locked/picoclock/3d-mini/screen_holder.scad

include <common.scad>;

border_width = 3;
border_height = 1.5;


module support() {
    cube(screen_holder_in, center=true);

    translate([0, 0]) cube([screen_holder_in[0], screen_holder_out[1], screen_holder_in[2]], center=true);
    // 2 holders

    // 4 screw supports
    $x = screen_holder_in[0]/2-screen_holder_out[0]/2;
    $y = -screen_holder_out[1]/2+screen_holder_out[0]/2;
    $z = -screen_holder_out[2];
    translate([$x, $y, $z])
        cube([screen_holder_out[0], screen_holder_out[0], screen_holder_out[2]], center=true);
    $y2 = screen_holder_out[1]/2-screen_holder_out[0]/2;
    translate([$x, $y2, $z])
        cube([screen_holder_out[0], screen_holder_out[0], screen_holder_out[2]], center=true);
    translate([-screen_holder_in[0]/2+screen_holder_out[0]/2, -screen_holder_out[1]/2+screen_holder_out[0]/2, -screen_holder_out[2]])
        cube([screen_holder_out[0], screen_holder_out[0], screen_holder_out[2]], center=true);
    translate([-screen_holder_in[0]/2+screen_holder_out[0]/2, screen_holder_out[1]/2-screen_holder_out[0]/2, -screen_holder_out[2]])
        cube([screen_holder_out[0], screen_holder_out[0], screen_holder_out[2]], center=true);

    // Support for printing
    for (x = [0:3]) {
        $posy = x < 2 ? -screen_holder_out[1]/2 + screen_holder_out[0]: screen_holder_out[1]/2;
        $mirrorz = x % 2 == 0 ? 1 : 0;
        mirror([$mirrorz,0,0])
            translate([
                -screen_holder_in[0]/2+screen_holder_out[0],
                $posy,
                -screen_holder_out[2]/2])
                rotate([90, 90])
                    linear_extrude(screen_holder_out[0])
                        polygon(points=[[0,0], [screen_holder_out[2], 0], [0, screen_holder_out[0]-1]], paths=[[0,1,2]]);
    }

    // Pins toward PCB
    for (x = [0:1]) {
        for (y = [0:1]) {
            translate([
                (x == 0 ? 1 : -1) * screen_holder_in[0]/2 + (x == 0 ? -1 : 1) * screen_holder_out[0]/2,
                (y == 0 ? 1 : -1) * screen_holder_out[1]/2 + (y == 0 ? -1 : 1) * screen_holder_screw_rad + (y == 0 ? -1 : 1) * 1,
                -screen_holder_out[2]-2-1.5])
            cylinder(h=2, d=1.9, $fn=20);
        }
    }

    // Blocks for case pins
    case_pin_height = 3.5;
    difference() {
        union() {
            for (x = [0:1]) {
                for (y = [0:1]) {
                    translate([
                        (x == 0 ? 1 : -1) * screen_holder_in[0]/2 + (x == 0 ? -1 : 1) * screen_holder_out[0]/2,
                        (y == 0 ? 1 : -1) * screen_holder_out[1]/2 + (y == 0 ? -1 : 1) * screen_holder_screw_rad + (y == 0 ? -1 : 1) * 1,
                        0])
                    cylinder(h=case_pin_height, d=4, $fn=20);
                }
            }
        }
        for (x = [0:1]) {
            for (y = [0:1]) {
                translate([
                    (x == 0 ? 1 : -1) * screen_holder_in[0]/2 + (x == 0 ? -1 : 1) * screen_holder_out[0]/2,
                    (y == 0 ? 1 : -1) * screen_holder_out[1]/2 + (y == 0 ? -1 : 1) * screen_holder_screw_rad + (y == 0 ? -1 : 1) * 1,
                    0])
                cylinder(h=case_pin_height, d=2.2, $fn=20);
            }
        }
    }

    // Borders
    translate([
        -screen_holder_in[0]/2,
        -screen_visible_size[1]/2-border_width*2,
        screen_holder_in[2]/2
    ])
        cube([screen_holder_in[0], border_width*2, border_height]);
    translate([
        -screen_holder_in[0]/2,
        screen_visible_size[1]/2,
        screen_holder_in[2]/2
    ])
        cube([screen_holder_in[0], border_width, border_height]);
    translate([
        screen_holder_in[0]/2-8.2,
        -screen_visible_size[1]/2,
        screen_holder_in[2]/2
    ])
        cube([border_width, screen_visible_size[1], border_height]);
    /*translate([
        -screen_visible_size[0]/2-border_width,
        -screen_visible_size[1]/2,
        screen_holder_in[2]/2
    ])
        cube([border_width, screen_visible_size[1], border_height]);*/
}

module screen_holder() {
    difference() {
        support();

        translate([-screen_size_toborder/2-2, 0, 0]) cube([
			screen_size[0]+screen_size_toborder,
			screen_size[1],
			screen_size[2]
		], center=true);

		// Opening to slide the screen
        translate([-screen_size[0]/2-screen_size_toborder/2, 0, -2])
            cube([screen_size_toborder, screen_size[1], 4], center=true);

        // Visible screen size
        translate([0, 0, 1]) cube(screen_visible_size, center=true);

        // Remove material on the left to ease printing
        translate([-screen_holder_in[0]/2+5, 0, 1]) cube([10, screen_visible_size[1], screen_visible_size[2]], center=true);

        // Light guide
        translate([23.5, -11, 4])
                rotate([180, 90])
                    linear_extrude(screen_holder_out[1]-7)
                        polygon(points=[[-0.3,0], [6, 5], [6, 15]], paths=[[0,1,2]]);
        translate([26, -11, 4])
                rotate([180, 90])
                    linear_extrude(screen_holder_out[1]-2)
                        polygon(points=[[-1.2,0], [0,0], [6, 5], [6, 9.6]], paths=[[0,1,2,3]]);
    }

    // Light shade
    light_shade_width = 0.5;
    translate([0, -screen_size[1]/2 - light_shade_width/2, 1])
        cube([screen_holder_in[0], light_shade_width, 4], center=true);

    // border left
    translate([
        -screen_visible_size[0]/2-border_width,
        -screen_visible_size[1]/2,
        screen_holder_in[2]/2-1.25
    ])
        cube([border_width, screen_visible_size[1], border_height+1.25]);
}

screen_holder();
