locked/picoclock/3d/button.scad

include <common.scad>;

outer_diam = 4.4;   // pcb holes are 5mm
depth = 6 + 1.6 + 1;

//btn_size = 2.4;	// Ok, tight
btn_size = 2.5;	// Ok, loose
btn = [btn_size, btn_size, 3];
fente = [1.3, 0.5, 3];

module body() {
    cylinder(h=4, d=outer_diam+0.5, $fn=30);
    cylinder(h=depth, d=outer_diam, $fn=30);
    translate([0, 0, depth]) cylinder(h=1, d=outer_diam+2, $fn=50);
}

difference() {
    body();
    translate([0, 0, btn[2]/2]) cube(btn, center=true);
    translate([-btn[0]/2-fente[0]/2, 0, fente[2]/2]) cube(fente, center=true);
    translate([+btn[0]/2+fente[0]/2, 0, fente[2]/2]) cube(fente, center=true);
}
