locked/picoclock/fw/rtos/platform/raspberry-pico-w/pwm_sound_melodies.h

note_struct HappyBirday[]={
    { NOTE_C4,4 },
    { NOTE_C4,8 },
    { NOTE_D4,-4},
    { NOTE_C4,-4},
    { NOTE_F4,-4},
    { NOTE_E4,-2},
    { NOTE_C4,4},
    {NOTE_C4,8},
    {NOTE_D4,-4},
    {NOTE_C4,-4},
    {NOTE_G4,-4},
    {NOTE_F4,-2},
    {NOTE_C4,4},
    {NOTE_C4,8},
    {NOTE_C5,-4},
    {NOTE_A4,-4},
    {NOTE_F4,-4},
    {NOTE_E4,-4},
    {NOTE_D4,-4},
    {NOTE_AS4,4},
    {NOTE_AS4,8},
    {NOTE_A4,-4},
    {NOTE_F4,-4},
    {NOTE_G4,-4},
    {NOTE_F4,-2},
    {REST,0}};


note_struct HarryPotter[]={
 // Hedwig's theme fromn the Harry Potter Movies
  // Socre from https://musescore.com/user/3811306/scores/4906610

  { REST, 2}, { NOTE_D4, 4},{ NOTE_G4, -4}, { NOTE_AS4, 8}, { NOTE_A4, 4},
  { NOTE_G4, 2}, { NOTE_D5, 4},{ NOTE_C5, -2}, { NOTE_A4, -2},
  { NOTE_G4, -4}, { NOTE_AS4, 8}, { NOTE_A4, 4},
  { NOTE_F4, 2}, { NOTE_GS4, 4},
  { NOTE_D4, -1}, { NOTE_D4, 4},

  { NOTE_G4, -4}, { NOTE_AS4, 8}, { NOTE_A4, 4},
  { NOTE_G4, 2}, { NOTE_D5, 4},
  { NOTE_F5, 2}, { NOTE_E5, 4},
  { NOTE_DS5, 2}, { NOTE_B4, 4},
  { NOTE_DS5, -4}, { NOTE_D5, 8}, { NOTE_CS5, 4},
  { NOTE_CS4, 2}, { NOTE_B4, 4},
  { NOTE_G4, -1},
  { NOTE_AS4, 4},

  { NOTE_D5, 2}, { NOTE_AS4, 4},
  { NOTE_D5, 2}, { NOTE_AS4, 4},
  { NOTE_DS5, 2}, { NOTE_D5, 4},
  { NOTE_CS5, 2}, { NOTE_A4, 4},
  { NOTE_AS4, -4}, { NOTE_D5, 8}, { NOTE_CS5, 4},
  { NOTE_CS4, 2}, { NOTE_D4, 4},
  { NOTE_D5, -1},
  {REST,4}, { NOTE_AS4,4},

  { NOTE_D5, 2}, { NOTE_AS4, 4},
  { NOTE_D5, 2}, { NOTE_AS4, 4},
  { NOTE_F5, 2}, { NOTE_E5, 4},
  { NOTE_DS5, 2}, { NOTE_B4, 4},
  { NOTE_DS5, -4}, { NOTE_D5, 8}, { NOTE_CS5, 4},
  { NOTE_CS4, 2}, { NOTE_AS4, 4},
  { NOTE_G4, -1}};



//
// Copied from https://github.com/twisst/pico-songs/blob/main/melodies.py
// => need convertion to this file format
//
// Star Trek intro
// Score available at https://musescore.com/user/10768291/scores/4594271
// notes = ['Star Trek intro', 80, 'NOTE_D4', '-8', 'NOTE_G4', '16', 'NOTE_C5', '-4', 'NOTE_B4', '8', 'NOTE_G4', '-16', 'NOTE_E4', '-16', 'NOTE_A4', '-16', 'NOTE_D5', '2']
// Silent Night
// Score available at https://musescore.com/marcsabatella/scores/3123436
// notes = ['Silent Night', 140, 'NOTE_G4', '-4', 'NOTE_A4', '8', 'NOTE_G4', '4', 'NOTE_E4', '-2', 'NOTE_G4', '-4', 'NOTE_A4', '8', 'NOTE_G4', '4', 'NOTE_E4', '-2', 'NOTE_D5', '2', 'NOTE_D5', '4', 'NOTE_B4', '-2', 'NOTE_C5', '2', 'NOTE_C5', '4', 'NOTE_G4', '-2', 'NOTE_A4', '2', 'NOTE_A4', '4', 'NOTE_C5', '-4', 'NOTE_B4', '8', 'NOTE_A4', '4', 'NOTE_G4', '-4', 'NOTE_A4', '8', 'NOTE_G4', '4', 'NOTE_E4', '-2', 'NOTE_A4', '2', 'NOTE_A4', '4', 'NOTE_C5', '-4', 'NOTE_B4', '8', 'NOTE_A4', '4', 'NOTE_G4', '-4', 'NOTE_A4', '8', 'NOTE_G4', '4', 'NOTE_E4', '-2', 'NOTE_D5', '2', 'NOTE_D5', '4', 'NOTE_F5', '-4', 'NOTE_D5', '8', 'NOTE_B4', '4', 'NOTE_C5', '-2', 'NOTE_E5', '-2', 'NOTE_C5', '4', 'NOTE_G4', '4', 'NOTE_E4', '4', 'NOTE_G4', '-4', 'NOTE_F4', '8', 'NOTE_D4', '4', 'NOTE_C4', '-2', 'NOTE_C4', '-1']
// Pacman
// Score available at https://musescore.com/user/85429/scores/107109
// notes = ['Pacman', 105, 'NOTE_B4', '16', 'NOTE_B5', '16', 'NOTE_FS5', '16', 'NOTE_DS5', '16', 'NOTE_B5', '32', 'NOTE_FS5', '-16', 'NOTE_DS5', '8', 'NOTE_C5', '16', 'NOTE_C6', '16', 'NOTE_G6', '16', 'NOTE_E6', '16', 'NOTE_C6', '32', 'NOTE_G6', '-16', 'NOTE_E6', '8', 'NOTE_B4', '16', 'NOTE_B5', '16', 'NOTE_FS5', '16', 'NOTE_DS5', '16', 'NOTE_B5', '32', 'NOTE_FS5', '-16', 'NOTE_DS5', '8', 'NOTE_DS5', '32', 'NOTE_E5', '32', 'NOTE_F5', '32', 'NOTE_F5', '32', 'NOTE_FS5', '32', 'NOTE_G5', '32', 'NOTE_G5', '32', 'NOTE_GS5', '32', 'NOTE_A5', '16', 'NOTE_B5', '8']
// Ode an die Freude - Beethoven's Symphony No. 9 
// notes = ['Ode an die Freude', 114, 'NOTE_E4', '4', 'NOTE_E4', '4', 'NOTE_F4', '4', 'NOTE_G4', '4', 'NOTE_G4', '4', 'NOTE_F4', '4', 'NOTE_E4', '4', 'NOTE_D4', '4', 'NOTE_C4', '4', 'NOTE_C4', '4', 'NOTE_D4', '4', 'NOTE_E4', '4', 'NOTE_E4', '-4', 'NOTE_D4', '8', 'NOTE_D4', '2', 'NOTE_E4', '4', 'NOTE_E4', '4', 'NOTE_F4', '4', 'NOTE_G4', '4', 'NOTE_G4', '4', 'NOTE_F4', '4', 'NOTE_E4', '4', 'NOTE_D4', '4', 'NOTE_C4', '4', 'NOTE_C4', '4', 'NOTE_D4', '4', 'NOTE_E4', '4', 'NOTE_D4', '-4', 'NOTE_C4', '8', 'NOTE_C4', '2', 'NOTE_D4', '4', 'NOTE_D4', '4', 'NOTE_E4', '4', 'NOTE_C4', '4', 'NOTE_D4', '4', 'NOTE_E4', '8', 'NOTE_F4', '8', 'NOTE_E4', '4', 'NOTE_C4', '4', 'NOTE_D4', '4', 'NOTE_E4', '8', 'NOTE_F4', '8', 'NOTE_E4', '4', 'NOTE_D4', '4', 'NOTE_C4', '4', 'NOTE_D4', '4', 'NOTE_G3', '2', 'NOTE_E4', '4', 'NOTE_E4', '4', 'NOTE_F4', '4', 'NOTE_G4', '4', 'NOTE_G4', '4', 'NOTE_F4', '4', 'NOTE_E4', '4', 'NOTE_D4', '4', 'NOTE_C4', '4', 'NOTE_C4', '4', 'NOTE_D4', '4', 'NOTE_E4', '4', 'NOTE_D4', '-4', 'NOTE_C4', '8', 'NOTE_C4', '2']
// Star Wars theme
// notes = ['Star Wars theme', 108, 'NOTE_AS4', '8', 'NOTE_AS4', '8', 'NOTE_AS4', '8', 'NOTE_F5', '2', 'NOTE_C6', '2', 'NOTE_AS5', '8', 'NOTE_A5', '8', 'NOTE_G5', '8', 'NOTE_F6', '2', 'NOTE_C6', '4', 'NOTE_AS5', '8', 'NOTE_A5', '8', 'NOTE_G5', '8', 'NOTE_F6', '2', 'NOTE_C6', '4', 'NOTE_AS5', '8', 'NOTE_A5', '8', 'NOTE_AS5', '8', 'NOTE_G5', '2', 'NOTE_C5', '8', 'NOTE_C5', '8', 'NOTE_C5', '8', 'NOTE_F5', '2', 'NOTE_C6', '2', 'NOTE_AS5', '8', 'NOTE_A5', '8', 'NOTE_G5', '8', 'NOTE_F6', '2', 'NOTE_C6', '4', 'NOTE_AS5', '8', 'NOTE_A5', '8', 'NOTE_G5', '8', 'NOTE_F6', '2', 'NOTE_C6', '4', 'NOTE_AS5', '8', 'NOTE_A5', '8', 'NOTE_AS5', '8', 'NOTE_G5', '2', 'NOTE_C5', '-8', 'NOTE_C5', '16', 'NOTE_D5', '-4', 'NOTE_D5', '8', 'NOTE_AS5', '8', 'NOTE_A5', '8', 'NOTE_G5', '8', 'NOTE_F5', '8', 'NOTE_F5', '8', 'NOTE_G5', '8', 'NOTE_A5', '8', 'NOTE_G5', '4', 'NOTE_D5', '8', 'NOTE_E5', '4', 'NOTE_C5', '-8', 'NOTE_C5', '16', 'NOTE_D5', '-4', 'NOTE_D5', '8', 'NOTE_AS5', '8', 'NOTE_A5', '8', 'NOTE_G5', '8', 'NOTE_F5', '8', 'NOTE_C6', '-8', 'NOTE_G5', '16', 'NOTE_G5', '2', 'REST', '8', 'NOTE_C5', '8', 'NOTE_D5', '-4', 'NOTE_D5', '8', 'NOTE_AS5', '8', 'NOTE_A5', '8', 'NOTE_G5', '8', 'NOTE_F5', '8', 'NOTE_F5', '8', 'NOTE_G5', '8', 'NOTE_A5', '8', 'NOTE_G5', '4', 'NOTE_D5', '8', 'NOTE_E5', '4', 'NOTE_C6', '-8', 'NOTE_C6', '16', 'NOTE_F6', '4', 'NOTE_DS6', '8', 'NOTE_CS6', '4', 'NOTE_C6', '8', 'NOTE_AS5', '4', 'NOTE_GS5', '8', 'NOTE_G5', '4', 'NOTE_F5', '8', 'NOTE_C6', '1']
// Wiegenlied (Brahms' Lullaby)
// Score available at https://www.flutetunes.com/tunes.php?id=54
// notes = ['Wiegenlied (Brahms\' Lullaby)', 76, 'NOTE_G4', '4', 'NOTE_G4', '4', 'NOTE_AS4', '-4', 'NOTE_G4', '8', 'NOTE_G4', '4', 'NOTE_AS4', '4', 'REST', '4', 'NOTE_G4', '8', 'NOTE_AS4', '8', 'NOTE_DS5', '4', 'NOTE_D5', '-4', 'NOTE_C5', '8', 'NOTE_C5', '4', 'NOTE_AS4', '4', 'NOTE_F4', '8', 'NOTE_G4', '8', 'NOTE_GS4', '4', 'NOTE_F4', '4', 'NOTE_F4', '8', 'NOTE_G4', '8', 'NOTE_GS4', '4', 'REST', '4', 'NOTE_F4', '8', 'NOTE_GS4', '8', 'NOTE_D5', '8', 'NOTE_C5', '8', 'NOTE_AS4', '4', 'NOTE_D5', '4', 'NOTE_DS5', '4', 'REST', '4', 'NOTE_DS4', '8', 'NOTE_DS4', '8', 'NOTE_DS5', '2', 'NOTE_C5', '8', 'NOTE_GS4', '8', 'NOTE_AS4', '2', 'NOTE_G4', '8', 'NOTE_DS4', '8', 'NOTE_GS4', '4', 'NOTE_AS4', '4', 'NOTE_C5', '4', 'NOTE_AS4', '2', 'NOTE_DS4', '8', 'NOTE_DS4', '8', 'NOTE_DS5', '2', 'NOTE_C5', '8', 'NOTE_GS4', '8', 'NOTE_AS4', '2', 'NOTE_G4', '8', 'NOTE_DS4', '8', 'NOTE_AS4', '4', 'NOTE_G4', '4', 'NOTE_DS4', '4', 'NOTE_DS4', '2']
// Theme A from Tetris (Korobeiniki)
// Based on the arrangement at https://www.flutetunes.com/tunes.php?id=192
// notes = ['Theme A from Tetris (Korobeiniki)', 144, 'NOTE_E5', '4', 'NOTE_B4', '8', 'NOTE_C5', '8', 'NOTE_D5', '4', 'NOTE_C5', '8', 'NOTE_B4', '8', 'NOTE_A4', '4', 'NOTE_A4', '8', 'NOTE_C5', '8', 'NOTE_E5', '4', 'NOTE_D5', '8', 'NOTE_C5', '8', 'NOTE_B4', '-4', 'NOTE_C5', '8', 'NOTE_D5', '4', 'NOTE_E5', '4', 'NOTE_C5', '4', 'NOTE_A4', '4', 'NOTE_A4', '8', 'NOTE_A4', '4', 'NOTE_B4', '8', 'NOTE_C5', '8', 'NOTE_D5', '-4', 'NOTE_F5', '8', 'NOTE_A5', '4', 'NOTE_G5', '8', 'NOTE_F5', '8', 'NOTE_E5', '-4', 'NOTE_C5', '8', 'NOTE_E5', '4', 'NOTE_D5', '8', 'NOTE_C5', '8', 'NOTE_B4', '4', 'NOTE_B4', '8', 'NOTE_C5', '8', 'NOTE_D5', '4', 'NOTE_E5', '4', 'NOTE_C5', '4', 'NOTE_A4', '4', 'NOTE_A4', '4', 'REST', '4', 'NOTE_E5', '4', 'NOTE_B4', '8', 'NOTE_C5', '8', 'NOTE_D5', '4', 'NOTE_C5', '8', 'NOTE_B4', '8', 'NOTE_A4', '4', 'NOTE_A4', '8', 'NOTE_C5', '8', 'NOTE_E5', '4', 'NOTE_D5', '8', 'NOTE_C5', '8', 'NOTE_B4', '-4', 'NOTE_C5', '8', 'NOTE_D5', '4', 'NOTE_E5', '4', 'NOTE_C5', '4', 'NOTE_A4', '4', 'NOTE_A4', '8', 'NOTE_A4', '4', 'NOTE_B4', '8', 'NOTE_C5', '8', 'NOTE_D5', '-4', 'NOTE_F5', '8', 'NOTE_A5', '4', 'NOTE_G5', '8', 'NOTE_F5', '8', 'NOTE_E5', '-4', 'NOTE_C5', '8', 'NOTE_E5', '4', 'NOTE_D5', '8', 'NOTE_C5', '8', 'NOTE_B4', '4', 'NOTE_B4', '8', 'NOTE_C5', '8', 'NOTE_D5', '4', 'NOTE_E5', '4', 'NOTE_C5', '4', 'NOTE_A4', '4', 'NOTE_A4', '4', 'REST', '4', 'NOTE_E5', '2', 'NOTE_C5', '2', 'NOTE_D5', '2', 'NOTE_B4', '2', 'NOTE_C5', '2', 'NOTE_A4', '2', 'NOTE_GS4', '2', 'NOTE_B4', '4', 'REST', '8', 'NOTE_E5', '2', 'NOTE_C5', '2', 'NOTE_D5', '2', 'NOTE_B4', '2', 'NOTE_C5', '4', 'NOTE_E5', '4', 'NOTE_A5', '2', 'NOTE_GS5', '2']
// Happy Birthday
// Score available at https://musescore.com/user/8221/scores/26906
// notes = ['Happy Birthday', 140, 'NOTE_C4', '4', 'NOTE_C4', '8', 'NOTE_D4', '-4', 'NOTE_C4', '-4', 'NOTE_F4', '-4', 'NOTE_E4', '-2', 'NOTE_C4', '4', 'NOTE_C4', '8', 'NOTE_D4', '-4', 'NOTE_C4', '-4', 'NOTE_G4', '-4', 'NOTE_F4', '-2', 'NOTE_C4', '4', 'NOTE_C4', '8', 'NOTE_C5', '-4', 'NOTE_A4', '-4', 'NOTE_F4', '-4', 'NOTE_E4', '-4', 'NOTE_D4', '-4', 'NOTE_AS4', '4', 'NOTE_AS4', '8', 'NOTE_A4', '-4', 'NOTE_F4', '-4', 'NOTE_G4', '-4', 'NOTE_F4', '-2']
// Darth Vader theme (Imperial March) - Star wars
// Score available at https://musescore.com/user/202909/scores/1141521
// The tenor saxophone part was used
// notes = ['Dart Vader theme', 120, 'NOTE_A4', '-4', 'NOTE_A4', '-4', 'NOTE_A4', '16', 'NOTE_A4', '16', 'NOTE_A4', '16', 'NOTE_A4', '16', 'NOTE_F4', '8', 'REST', '8', 'NOTE_A4', '-4', 'NOTE_A4', '-4', 'NOTE_A4', '16', 'NOTE_A4', '16', 'NOTE_A4', '16', 'NOTE_A4', '16', 'NOTE_F4', '8', 'REST', '8', 'NOTE_A4', '4', 'NOTE_A4', '4', 'NOTE_A4', '4', 'NOTE_F4', '-8', 'NOTE_C5', '16', 'NOTE_A4', '4', 'NOTE_F4', '-8', 'NOTE_C5', '16', 'NOTE_A4', '2', 'NOTE_E5', '4', 'NOTE_E5', '4', 'NOTE_E5', '4', 'NOTE_F5', '-8', 'NOTE_C5', '16', 'NOTE_A4', '4', 'NOTE_F4', '-8', 'NOTE_C5', '16', 'NOTE_A4', '2', 'NOTE_A5', '4', 'NOTE_A4', '-8', 'NOTE_A4', '16', 'NOTE_A5', '4', 'NOTE_GS5', '-8', 'NOTE_G5', '16', 'NOTE_DS5', '16', 'NOTE_D5', '16', 'NOTE_DS5', '8', 'REST', '8', 'NOTE_A4', '8', 'NOTE_DS5', '4', 'NOTE_D5', '-8', 'NOTE_CS5', '16', 'NOTE_C5', '16', 'NOTE_B4', '16', 'NOTE_C5', '16', 'REST', '8', 'NOTE_F4', '8', 'NOTE_GS4', '4', 'NOTE_F4', '-8', 'NOTE_A4', '-16', 'NOTE_C5', '4', 'NOTE_A4', '-8', 'NOTE_C5', '16', 'NOTE_E5', '2', 'NOTE_A5', '4', 'NOTE_A4', '-8', 'NOTE_A4', '16', 'NOTE_A5', '4', 'NOTE_GS5', '-8', 'NOTE_G5', '16', 'NOTE_DS5', '16', 'NOTE_D5', '16', 'NOTE_DS5', '8', 'REST', '8', 'NOTE_A4', '8', 'NOTE_DS5', '4', 'NOTE_D5', '-8', 'NOTE_CS5', '16', 'NOTE_C5', '16', 'NOTE_B4', '16', 'NOTE_C5', '16', 'REST', '8', 'NOTE_F4', '8', 'NOTE_GS4', '4', 'NOTE_F4', '-8', 'NOTE_A4', '-16', 'NOTE_A4', '4', 'NOTE_F4', '-8', 'NOTE_C5', '16', 'NOTE_A4', '2']
// Nokia Ringtone
// Score available at https://musescore.com/user/29944637/scores/5266155
// notes = ['Nokia Ringtone', 180, 'NOTE_E5', '8', 'NOTE_D5', '8', 'NOTE_FS4', '4', 'NOTE_GS4', '4', 'NOTE_CS5', '8', 'NOTE_B4', '8', 'NOTE_D4', '4', 'NOTE_E4', '4', 'NOTE_B4', '8', 'NOTE_A4', '8', 'NOTE_CS4', '4', 'NOTE_E4', '4', 'NOTE_A4', '2']
// Mii Channel theme
// Score available at https://musescore.com/user/16403456/scores/4984153
// notes = ['Mii Channel theme', 114, 'NOTE_FS4', '8', 'REST', '8', 'NOTE_A4', '8', 'NOTE_CS5', '8', 'REST', '8', 'NOTE_A4', '8', 'REST', '8', 'NOTE_FS4', '8', 'NOTE_D4', '8', 'NOTE_D4', '8', 'NOTE_D4', '8', 'REST', '8', 'REST', '4', 'REST', '8', 'NOTE_CS4', '8', 'NOTE_D4', '8', 'NOTE_FS4', '8', 'NO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
// Minuet in G - Petzold
// Score available at https://musescore.com/user/3402766/scores/1456391
// notes = ['Minuet in G - Petzold', 140, 'NOTE_D5', '4', 'NOTE_G4', '8', 'NOTE_A4', '8', 'NOTE_B4', '8', 'NOTE_C5', '8', 'NOTE_D5', '4', 'NOTE_G4', '4', 'NOTE_G4', '4', 'NOTE_E5', '4', 'NOTE_C5', '8', 'NOTE_D5', '8', 'NOTE_E5', '8', 'NOTE_FS5', '8', 'NOTE_G5', '4', 'NOTE_G4', '4', 'NOTE_G4', '4', '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
// Badinerie - Johann Sebastian Bach
// notes = ['Badinerie - Johann Sebastian Bach', 120, 'NOTE_B5', '-8', 'NOTE_D6', '16', 'NOTE_B5', '16', 'NOTE_FS5', '-8', 'NOTE_B5', '16', 'NOTE_FS5', '16', 'NOTE_D5', '-8', 'NOTE_FS5', '16', 'NOTE_D5', '16', 'NOTE_B4', '4', 'NOTE_F4', '16', 'NOTE_B4', '16', 'NOTE_D5', '16', 'NOTE_B4', '16', 'NOTE_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
// Für Elise - Ludwig van Beethoven
// Score available at https://musescore.com/user/28149610/scores/5281944
// notes = ['Für Elise - Ludwig van Beethoven', 80, 'NOTE_E5', '16', 'NOTE_DS5', '16', 'NOTE_E5', '16', 'NOTE_DS5', '16', 'NOTE_E5', '16', 'NOTE_B4', '16', 'NOTE_D5', '16', 'NOTE_C5', '16', 'NOTE_A4', '-8', 'NOTE_C4', '16', 'NOTE_E4', '16', 'NOTE_A4', '16', 'NOTE_B4', '-8', 'NOTE_E4', '16', 'NOTE_GS4', '16', 'NOTE_B4', '16', 'NOTE_C5', '8', 'REST', '16', 'NOTE_E4', '16', 'NOTE_E5', '16', 'NOTE_DS5', '16', 'NOTE_E5', '16', 'NOTE_DS5', '16', 'NOTE_E5', '16', 'NOTE_B4', '16', 'NOTE_D5', '16', 'NOTE_C5', '16', 'NOTE_A4', '-8', 'NOTE_C4', '16', 'NOTE_E4', '16', 'NOTE_A4', '16', 'NOTE_B4', '-8', 'NOTE_E4', '16', 'NOTE_C5', '16', 'NOTE_B4', '16', 'NOTE_A4', '4', 'REST', '8', 'NOTE_E5', '16', 'NOTE_DS5', '16', 'NOTE_E5', '16', 'NOTE_DS5', '16', 'NOTE_E5', '16', 'NOTE_B4', '16', 'NOTE_D5', '16', 'NOTE_C5', '16', 'NOTE_A4', '-8', 'NOTE_C4', '16', 'NOTE_E4', '16', 'NOTE_A4', '16', 'NOTE_B4', '-8', 'NOTE_E4', '16', 'NOTE_GS4', '16', 'NOTE_B4', '16', 'NOTE_C5', '8', 'REST', '16', 'NOTE_E4', '16', 'NOTE_E5', '16', 'NOTE_DS5', '16', 'NOTE_E5', '16', 'NOTE_DS5', '16', 'NOTE_E5', '16', 'NOTE_B4', '16', 'NOTE_D5', '16', 'NOTE_C5', '16', 'NOTE_A4', '-8', 'NOTE_C4', '16', 'NOTE_E4', '16', 'NOTE_A4', '16', 'NOTE_B4', '-8', 'NOTE_E4', '16', 'NOTE_C5', '16', 'NOTE_B4', '16', 'NOTE_A4', '8', 'REST', '16', 'NOTE_B4', '16', 'NOTE_C5', '16', 'NOTE_D5', '16', 'NOTE_E5', '-8', 'NOTE_G4', '16', 'NOTE_F5', '16', 'NOTE_E5', '16', 'NOTE_D5', '-8', 'NOTE_F4', '16', 'NOTE_E5', '16', 'NOTE_D5', '16', 'NOTE_C5',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
 '16', 'NOTE_B4', '16', 'NOTE_D5', '16', 'NOTE_C5', '16', 'NOTE_A4', '-8', 'NOTE_C4', '16', 'NOTE_E4', '16', 'NOTE_A4', '16', 'NOTE_B4', '-8', 'NOTE_E4', '16', 'NOTE_C5', '16', 'NOTE_B4', '16', 'NOTE_A4', '-8', 'REST', '-8', 'REST', '-8', 'NOTE_G4', '16', 'NOTE_F5', '16', 'NOTE_E5', '16', 'NOTE_D5', '4', 'REST', '8', 'REST', '-8', 'NOTE_E4', '16', 'NOTE_D5', '16', 'NOTE_C5', '16', 'NOTE_B4', '-8', 'NOTE_E4', '16', 'NOTE_E5', '8', 'NOTE_E5', '8', 'NOTE_E6', '-8', 'NOTE_DS5', '16', 'NOTE_E5', '16', 'REST', '16', 'REST', '16', 'NOTE_DS5', '16', 'NOTE_E5', '16', 'NOTE_DS5', '16', 'NOTE_E5', '16', 'NOTE_DS5', '16', 'NOTE_E5', '16', 'NOTE_B4', '16', 'NOTE_D5', '16', 'NOTE_C5', '16', 'NOTE_A4', '-8', 'NOTE_C4', '16', 'NOTE_E4', '16', 'NOTE_A4', '16', 'NOTE_B4', '-8', 'NOTE_E4', '16', 'NOTE_GS4', '16', 'NOTE_B4', '16', 'NOTE_C5', '8', 'REST', '16', 'NOTE_E4', '16', 'NOTE_E5', '16', 'NOTE_DS5', '16', 'NOTE_E5', '16', 'NOTE_DS5', '16', 'NOTE_E5', '16', 'NOTE_B4', '16', 'NOTE_D5', '16', 'NOTE_C5', '16', 'NOTE_A4', '-8', 'NOTE_C4', '16', 'NOTE_E4', '16', 'NOTE_A4', '16', 'NOTE_B4', '-8', 'NOTE_E4', '16', 'NOTE_C5', '16', 'NOTE_B4', '16', 'NOTE_A4', '-4']
// Cantina Band (Star wars)
// Score available at https://musescore.com/user/6795541/scores/1606876
// notes = ['Cantina Band (Star wars)', 140, 'NOTE_B4', '-4', 'NOTE_E5', '-4', 'NOTE_B4', '-4', 'NOTE_E5', '-4', 'NOTE_B4', '8', 'NOTE_E5', '-4', 'NOTE_B4', '8', 'REST', '8', 'NOTE_AS4', '8', 'NOTE_B4', '8', 'NOTE_B4', '8', 'NOTE_AS4', '8', 'NOTE_B4', '8', 'NOTE_A4', '8', 'REST', '8', 'NOTE_GS4', '8', 'NOTE_A4', '8', 'NOTE_G4', '8', 'NOTE_G4', '4', 'NOTE_E4', '-2', 'NOTE_B4', '-4', 'NOTE_E5', '-4', 'NOTE_B4', '-4', 'NOTE_E5', '-4', 'NOTE_B4', '8', 'NOTE_E5', '-4', 'NOTE_B4', '8', 'REST', '8', 'NOTE_AS4', '8', 'NOTE_B4', '8', 'NOTE_A4', '-4', 'NOTE_A4', '-4', 'NOTE_GS4', '8', 'NOTE_A4', '-4', 'NOTE_D5', '8', 'NOTE_C5', '-4', 'NOTE_B4', '-4', 'NOTE_A4', '-4', 'NOTE_B4', '-4', 'NOTE_E5', '-4', 'NOTE_B4', '-4', 'NOTE_E5', '-4', 'NOTE_B4', '8', 'NOTE_E5', '-4', 'NOTE_B4', '8', 'REST', '8', 'NOTE_AS4', '8', 'NOTE_B4', '8', 'NOTE_D5', '4', 'NOTE_D5', '-4', 'NOTE_B4', '8', 'NOTE_A4', '-4', 'NOTE_G4', '-4', 'NOTE_E4', '-2', 'NOTE_E4', '2', 'NOTE_G4', '2', 'NOTE_B4', '2', 'NOTE_D5', '2', 'NOTE_F5', '-4', 'NOTE_E5', '-4', 'NOTE_AS4', '8', 'NOTE_AS4', '8', 'NOTE_B4', '4', 'NOTE_G4', '4']
// Song of storms (The Legend of Zelda, Ocarina of Time)
// Score available at https://musescore.com/user/4957541/scores/1545401
// notes = ['Song of storms (The Legend of Zelda, Ocarina of Time)', 108, 'NOTE_D4', '4', 'NOTE_A4', '4', 'NOTE_A4', '4', 'REST', '8', 'NOTE_E4', '8', 'NOTE_B4', '2', 'NOTE_F4', '4', 'NOTE_C5', '4', 'NOTE_C5', '4', 'REST', '8', 'NOTE_E4', '8', 'NOTE_B4', '2', 'NOTE_D4', '4', 'NOTE_A4', '4', 'NOTE_A4', '4', 'REST', '8', 'NOTE_E4', '8', 'NOTE_B4', '2', 'NOTE_F4', '4', 'NOTE_C5', '4', 'NOTE_C5', '4', 'REST', '8', 'NOTE_E4', '8', 'NOTE_B4', '2', 'NOTE_D4', '8', 'NOTE_F4', '8', 'NOTE_D5', '2', 'NOTE_D4', '8', 'NOTE_F4', '8', 'NOTE_D5', '2', 'NOTE_E5', '-4', 'NOTE_F5', '8', 'NOTE_E5', '8', 'NOTE_E5', '8', 'NOTE_E5', '8', 'NOTE_C5', '8', 'NOTE_A4', '2', 'NOTE_A4', '4', 'NOTE_D4', '4', 'NOTE_F4', '8', 'NOTE_G4', '8', 'NOTE_A4', '-2', 'NOTE_A4', '4', 'NOTE_D4', '4', 'NOTE_F4', '8', 'NOTE_G4', '8', 'NOTE_E4', '-2', 'NOTE_D4', '8', 'NOTE_F4', '8', 'NOTE_D5', '2', 'NOTE_D4', '8', 'NOTE_F4', '8', 'NOTE_D5', '2', 'NOTE_E5', '-4', 'NOTE_F5', '8', 'NOTE_E5', '8', 'NOTE_E5', '8', 'NOTE_E5', '8', 'NOTE_C5', '8', 'NOTE_A4', '2', 'NOTE_A4', '4', 'NOTE_D4', '4', 'NOTE_F4', '8', 'NOTE_G4', '8', 'NOTE_A4', '2', 'NOTE_A4', '4', 'NOTE_D4', '1']
// The Lion Sleeps Tonight
// Score available at https://musescore.com/user/18545446/scores/5061407
// notes = ['The Lion Sleeps Tonight', 122, 'NOTE_F4', '4', 'NOTE_G4', '4', 'NOTE_A4', '8', 'NOTE_G4', '4', 'NOTE_A4', '8', 'NOTE_AS4', '4', 'NOTE_A4', '4', 'NOTE_G4', '8', 'NOTE_F4', '4', 'NOTE_G4', '8', 'NOTE_A4', '4', 'NOTE_C4', '8', 'NOTE_C4', '4', 'NOTE_C4', '8', 'NOTE_C4', '4', 'NOTE_C4', '1',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
// The Lick
// notes = ['The Lick', 108, 'NOTE_D4', '8', 'NOTE_E4', '8', 'NOTE_F4', '8', 'NOTE_G4', '8', 'NOTE_E4', '4', 'NOTE_C4', '8', 'NOTE_D4', '1']
// Canon in D - Pachelbel
// Score available at https://musescore.com/user/4710311/scores/1975521
// notes = ['Canon in D - Pachelbel', 100, 'NOTE_FS4', '2', 'NOTE_E4', '2', 'NOTE_D4', '2', 'NOTE_CS4', '2', 'NOTE_B3', '2', 'NOTE_A3', '2', 'NOTE_B3', '2', 'NOTE_CS4', '2', 'NOTE_FS4', '2', 'NOTE_E4', '2', 'NOTE_D4', '2', 'NOTE_CS4', '2', 'NOTE_B3', '2', 'NOTE_A3', '2', 'NOTE_B3', '2', 'NOTE_CS4', '2', 'NOTE_D4', '2', 'NOTE_CS4', '2', 'NOTE_B3', '2', 'NOTE_A3', '2', 'NOTE_G3', '2', 'NOTE_FS3', '2', 'NOTE_G3', '2', 'NOTE_A3', '2', 'NOTE_D4', '4', 'NOTE_FS4', '8', 'NOTE_G4', '8', 'NOTE_A4', '4', 'NOTE_FS4', '8', 'NOTE_G4', '8', 'NOTE_A4', '4', 'NOTE_B3', '8', 'NOTE_CS4', '8', 'NOTE_D4', '8', 'NOTE_E4', '8', 'NOTE_FS4', '8', 'NOTE_G4', '8', 'NOTE_FS4', '4', 'NOTE_D4', '8', 'NOTE_E4', '8', 'NOTE_FS4', '4', 'NOTE_FS3', '8', 'NOTE_G3', '8', 'NOTE_A3', '8', 'NOTE_G3', '8', 'NOTE_FS3', '8', 'NOTE_G3', '8', 'NOTE_A3', '2', 'NOTE_G3', '4', 'NOTE_B3', '8', 'NOTE_A3', '8', 'NOTE_G3', '4', 'NOTE_FS3', '8', 'NOTE_E3', '8', 'NOTE_FS3', '4', 'NOTE_D3', '8', 'NOTE_E3', '8', 'NOTE_FS3', '8', 'NOTE_G3', '8', 'NOTE_A3', '8', 'NOTE_B3', '8', 'NOTE_G3', '4', 'NOTE_B3', '8', 'NOTE_A3', '8', 'NOTE_B3', '4', 'NOTE_CS4', '8', 'NOTE_D4', '8', 'NOTE_A3', '8', 'NOTE_B3', '8', 'NOTE_CS4', '8', 'NOTE_D4', '8', 'NOTE_E4', '8', 'NOTE_FS4', '8', 'NOTE_G4', '8', 'NOTE_A4', '2', 'NOTE_A4', '4', 'NOTE_FS4', '8', 'NOTE_G4', '8', 'NOTE_A4', '4', 'NOTE_FS4', '8', 'NOTE_G4', '8', 'NOTE_A4', '8', 'NOTE_A3', '8', 'NOTE_B3', '8', 'NOTE_CS4', '8', 'NOTE_D4', '8', 'NOTE_E4', '8', 'NOTE_FS4', '8', 'NOTE_G4', '8', 'NOTE_FS4', '4', 'NOTE_D4', '8', 'NOTE_E4', '8', 'NOTE_FS4', '8', 'NOTE_CS4', '8', 'NOTE_A3', '8', 'NOTE_A3', '8', 'NOTE_CS4', '4', 'NOTE_B3', '4', 'NOTE_D4', '8', 'NOTE_CS4', '8', 'NOTE_B3', '4', 'NOTE_A3', '8', 'NOTE_G3', '8', 'NOTE_A3', '4', 'NOTE_D3', '8', 'NOTE_E3', '8', 'NOTE_FS3', '8', 'NOTE_G3', '8', 'NOTE_A3', '8', 'NOTE_B3', '4', 'NOTE_G3', '4', 'NOTE_B3', '8', 'NOTE_A3', '8', 'NOTE_B3', '4', 'NOTE_CS4', '8', 'NOTE_D4', '8', 'NOTE_A3', '8', 'NOTE_B3', '8', 'NOTE_CS4', '8', 'NOTE_D4', '8', 'NOTE_E4', '8', 'NOTE_FS4', '8', 'NOTE_G4', '8', 'NOTE_A4', '2']
// At Doom's Gate (E1M1)
// Score available at https://musescore.com/pieridot/doom
// notes = ['At Doom\'s Gate (E1M1)', 225, 'NOTE_E2', '8', 'NOTE_E2', '8', 'NOTE_E3', '8', 'NOTE_E2', '8', 'NOTE_E2', '8', 'NOTE_D3', '8', 'NOTE_E2', '8', 'NOTE_E2', '8', 'NOTE_C3', '8', 'NOTE_E2', '8', 'NOTE_E2', '8', 'NOTE_AS2', '8', 'NOTE_E2', '8', 'NOTE_E2', '8', 'NOTE_B2', '8', 'NOTE_C3', '8', 'NOTE_E2', '8', 'NOTE_E2', '8', 'NOTE_E3', '8', 'NOTE_E2', '8', 'NOTE_E2', '8', 'NOTE_D3', '8', 'NOTE_E2', '8', 'NOTE_E2', '8', 'NOTE_C3', '8', 'NOTE_E2', '8', 'NOTE_E2', '8', 'NOTE_AS2', '-2', 'NOTE_E2', '8', 'NOTE_E2', '8', 'NOTE_E3', '8', 'NOTE_E2', '8', 'NOTE_E2', '8', 'NOTE_D3', '8', 'NOTE_E2', '8', 'NOTE_E2', '8', 'NOTE_C3', '8', 'NOTE_E2', '8', 'NOTE_E2', '8', 'NOTE_AS2', '8', 'NOTE_E2', '8', 'NOTE_E2', '8', 'NOTE_B2', '8', 'NOTE_C3', '8', 'NOTE_E2', '8', 'NOTE_E2', '8', 'NOTE_E3', '8', 'NOTE_E2', '8', 'NOTE_E2', '8', 'NOTE_D3', '8', 'NOTE_E2', '8', 'NOTE_E2', '8', 'NOTE_C3', '8', 'NOTE_E2', '8', 'NOTE_E2', '8', 'NOTE_AS2', '-2', 'NOTE_E2', '8', 'NOTE_E2', '8', 'NOTE_E3', '8', 'NOTE_E2', '8', 'NOTE_E2', '8', 'NOTE_D3', '8', 'NOTE_E2', '8', 'NOTE_E2', '8', 'NOTE_C3', '8', 'NOTE_E2', '8', 'NOTE_E2', '8', 'NOTE_AS2', '8', 'NOTE_E2', '8', 'NOTE_E2', '8', 'NOTE_B2', '8', 'NOTE_C3', '8', 'NOTE_E2', '8', 'NOTE_E2', '8', 'NOTE_E3', '8', 'NOTE_E2', '8', 'NOTE_E2', '8', 'NOTE_D3', '8', 'NOTE_E2', '8', 'NOTE_E2', '8', 'NOTE_C3', '8', 'NOTE_E2', '8', 'NOTE_E2', '8', 'NOTE_AS2', '-2', 'NOTE_E2', '8', 'NOTE_E2', '8', 'NOTE_E3', '8', 'NOTE_E2', '8', 'NOTE_E2', '8', 'NOTE_D3', '8', 'NOTE_E2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
// Pink Panther theme
// Score available at https://musescore.com/benedictsong/the-pink-panther
// notes = ['Pink Panther theme', 120, 'REST', '2', 'REST', '4', 'REST', '8', 'NOTE_DS4', '8', 'NOTE_E4', '-4', 'REST', '8', 'NOTE_FS4', '8', 'NOTE_G4', '-4', 'REST', '8', 'NOTE_DS4', '8', 'NOTE_E4', '-8', 'NOTE_FS4', '8', 'NOTE_G4', '-8', 'NOTE_C5', '8', 'NOTE_B4', '-8', 'NOTE_E4', '8', 'NOTE_G4', '-8', 'NOTE_B4', '8', 'NOTE_AS4', '2', 'NOTE_A4', '-16', 'NOTE_G4', '-16', 'NOTE_E4', '-16', 'NOTE_D4', '-16', 'NOTE_E4', '2', 'REST', '4', 'REST', '8', 'NOTE_DS4', '4', 'NOTE_E4', '-4', 'REST', '8', 'NOTE_FS4', '8', 'NOTE_G4', '-4', 'REST', '8', 'NOTE_DS4', '8', 'NOTE_E4', '-8', 'NOTE_FS4', '8', 'NOTE_G4', '-8', 'NOTE_C5', '8', 'NOTE_B4', '-8', 'NOTE_G4', '8', 'NOTE_B4', '-8', 'NOTE_E5', '8', 'NOTE_DS5', '1', 'NOTE_D5', '2', 'REST', '4', 'REST', '8', 'NOTE_DS4', '8', 'NOTE_E4', '-4', 'REST', '8', 'NOTE_FS4', '8', 'NOTE_G4', '-4', 'REST', '8', 'NOTE_DS4', '8', 'NOTE_E4', '-8', 'NOTE_FS4', '8', 'NOTE_G4', '-8', 'NOTE_C5', '8', 'NOTE_B4', '-8', 'NOTE_E4', '8', 'NOTE_G4', '-8', 'NOTE_B4', '8', 'NOTE_AS4', '2', 'NOTE_A4', '-16', 'NOTE_G4', '-16', 'NOTE_E4', '-16', 'NOTE_D4', '-16', 'NOTE_E4', '-4', 'REST', '4', 'REST', '4', 'NOTE_E5', '-8', 'NOTE_D5', '8', 'NOTE_B4', '-8', 'NOTE_A4', '8', 'NOTE_G4', '-8', 'NOTE_E4', '-8', 'NOTE_AS4', '16', 'NOTE_A4', '-8', 'NOTE_AS4', '16', 'NOTE_A4', '-8', 'NOTE_AS4', '16', 'NOTE_A4', '-8', 'NOTE_AS4', '16', 'NOTE_A4', '-8', 'NOTE_G4', '-16', 'NOTE_E4', '-16', 'NOTE_D4', '-16', 'NOTE_E4', '16', 'NOTE_E4', '16', 'NOTE_E4', '2']
// Hedwig's theme (Harry Potter)
// Socre from https://musescore.com/user/3811306/scores/4906610
// notes = ['Hedwig\'s theme (Harry Potter)', 144, 'REST', '2', 'NOTE_D4', '4', 'NOTE_G4', '-4', 'NOTE_AS4', '8', 'NOTE_A4', '4', 'NOTE_G4', '2', 'NOTE_D5', '4', 'NOTE_C5', '-2', 'NOTE_A4', '-2', 'NOTE_G4', '-4', 'NOTE_AS4', '8', 'NOTE_A4', '4', 'NOTE_F4', '2', 'NOTE_GS4', '4', 'NOTE_D4', '-1', 'NOTE_D4', '4', 'NOTE_G4', '-4', 'NOTE_AS4', '8', 'NOTE_A4', '4', 'NOTE_G4', '2', 'NOTE_D5', '4', 'NOTE_F5', '2', 'NOTE_E5', '4', 'NOTE_DS5', '2', 'NOTE_B4', '4', 'NOTE_DS5', '-4', 'NOTE_D5', '8', 'NOTE_CS5', '4', 'NOTE_CS4', '2', 'NOTE_B4', '4', 'NOTE_G4', '-1', 'NOTE_AS4', '4', 'NOTE_D5', '2', 'NOTE_AS4', '4', 'NOTE_D5', '2', 'NOTE_AS4', '4', 'NOTE_DS5', '2', 'NOTE_D5', '4', 'NOTE_CS5', '2', 'NOTE_A4', '4', 'NOTE_AS4', '-4', 'NOTE_D5', '8', 'NOTE_CS5', '4', 'NOTE_CS4', '2', 'NOTE_D4', '4', 'NOTE_D5', '-1', 'REST', '4', 'NOTE_AS4', '4', 'NOTE_D5', '2', 'NOTE_AS4', '4', 'NOTE_D5', '2', 'NOTE_AS4', '4', 'NOTE_F5', '2', 'NOTE_E5', '4', 'NOTE_DS5', '2', 'NOTE_B4', '4', 'NOTE_DS5', '-4', 'NOTE_D5', '8', 'NOTE_CS5', '4', 'NOTE_CS4', '2', 'NOTE_AS4', '4', 'NOTE_G4', '-1']
// Jigglypuff's Song
// Score available at https://musescore.com/user/28109683/scores/5044153
// notes = ['Jigglypuff\'s Song', 85, 'NOTE_D5', '-4', 'NOTE_A5', '8', 'NOTE_FS5', '8', 'NOTE_D5', '8', 'NOTE_E5', '-4', 'NOTE_FS5', '8', 'NOTE_G5', '4', 'NOTE_FS5', '-4', 'NOTE_E5', '8', 'NOTE_FS5', '4', 'NOTE_D5', '-2', 'NOTE_D5', '-4', 'NOTE_A5', '8', 'NOTE_FS5', '8', 'NOTE_D5', '8', 'NOTE_E5', '-4', 'NOTE_FS5', '8', 'NOTE_G5', '4', 'NOTE_FS5', '-1', 'NOTE_D5', '-4', 'NOTE_A5', '8', 'NOTE_FS5', '8', 'NOTE_D5', '8', 'NOTE_E5', '-4', 'NOTE_FS5', '8', 'NOTE_G5', '4', 'NOTE_FS5', '-4', 'NOTE_E5', '8', 'NOTE_FS5', '4', 'NOTE_D5', '-2', 'NOTE_D5', '-4', 'NOTE_A5', '8', 'NOTE_FS5', '8', 'NOTE_D5', '8', 'NOTE_E5', '-4', 'NOTE_FS5', '8', 'NOTE_G5', '4', 'NOTE_FS5', '-1']
// We Wish You a Merry Christmas
// Score available at https://musescore.com/user/6208766/scores/1497501
// notes = ['We Wish You a Merry Christmas', 140, 'NOTE_C5', '4', 'NOTE_F5', '4', 'NOTE_F5', '8', 'NOTE_G5', '8', 'NOTE_F5', '8', 'NOTE_E5', '8', 'NOTE_D5', '4', 'NOTE_D5', '4', 'NOTE_D5', '4', 'NOTE_G5', '4', 'NOTE_G5', '8', 'NOTE_A5', '8', 'NOTE_G5', '8', 'NOTE_F5', '8', 'NOTE_E5', '4', 'NOTE_C5',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
// Keyboard cat
// Score available at https://musescore.com/user/142788/scores/147371
// notes = ['Keyboard cat', 160, 'REST', '1', 'REST', '1', 'NOTE_C4', '4', 'NOTE_E4', '4', 'NOTE_G4', '4', 'NOTE_E4', '4', 'NOTE_C4', '4', 'NOTE_E4', '8', 'NOTE_G4', '-4', 'NOTE_E4', '4', 'NOTE_A3', '4', 'NOTE_C4', '4', 'NOTE_E4', '4', 'NOTE_C4', '4', 'NOTE_A3', '4', 'NOTE_C4', '8', 'NOTE_E4', '-4', 'NOTE_C4', '4', 'NOTE_G3', '4', 'NOTE_B3', '4', 'NOTE_D4', '4', 'NOTE_B3', '4', 'NOTE_G3', '4', 'NOTE_B3', '8', 'NOTE_D4', '-4', 'NOTE_B3', '4', 'NOTE_G3', '4', 'NOTE_G3', '8', 'NOTE_G3', '-4', 'NOTE_G3', '8', 'NOTE_G3', '4', 'NOTE_G3', '4', 'NOTE_G3', '4', 'NOTE_G3', '8', 'NOTE_G3', '4', 'NOTE_C4', '4', 'NOTE_E4', '4', 'NOTE_G4', '4', 'NOTE_E4', '4', 'NOTE_C4', '4', 'NOTE_E4', '8', 'NOTE_G4', '-4', 'NOTE_E4', '4', 'NOTE_A3', '4', 'NOTE_C4', '4', 'NOTE_E4', '4', 'NOTE_C4', '4', 'NOTE_A3', '4', 'NOTE_C4', '8', 'NOTE_E4', '-4', 'NOTE_C4', '4', 'NOTE_G3', '4', 'NOTE_B3', '4', 'NOTE_D4', '4', 'NOTE_B3', '4', 'NOTE_G3', '4', 'NOTE_B3', '8', 'NOTE_D4', '-4', 'NOTE_B3', '4', 'NOTE_G3', '-1']
// Game of Thrones
// Score available at https://musescore.com/user/8407786/scores/2156716
// notes = ['Game of Thrones', 85, 'NOTE_G4', '8', 'NOTE_C4', '8', 'NOTE_DS4', '16', 'NOTE_F4', '16', 'NOTE_G4', '8', 'NOTE_C4', '8', 'NOTE_DS4', '16', 'NOTE_F4', '16', 'NOTE_G4', '8', 'NOTE_C4', '8', 'NOTE_DS4', '16', 'NOTE_F4', '16', 'NOTE_G4', '8', 'NOTE_C4', '8', 'NOTE_DS4', '16', 'NOTE_F4', '16', 'NOTE_G4', '8', 'NOTE_C4', '8', 'NOTE_E4', '16', 'NOTE_F4', '16', 'NOTE_G4', '8', 'NOTE_C4', '8', 'NOTE_E4', '16', 'NOTE_F4', '16', 'NOTE_G4', '8', 'NOTE_C4', '8', 'NOTE_E4', '16', 'NOTE_F4', '16', 'NOTE_G4', '8', 'NOTE_C4', '8', 'NOTE_E4', '16', 'NOTE_F4', '16', 'NOTE_G4', '-4', 'NOTE_C4', '-4', 'NOTE_DS4', '16', 'NOTE_F4', '16', 'NOTE_G4', '4', 'NOTE_C4', '4', 'NOTE_DS4', '16', 'NOTE_F4', '16', 'NOTE_D4', '-1', 'NOTE_F4', '-4', 'NOTE_AS3', '-4', 'NOTE_DS4', '16', 'NOTE_D4', '16', 'NOTE_F4', '4', 'NOTE_AS3', '-4', 'NOTE_DS4', '16', 'NOTE_D4', '16', 'NOTE_C4', '-1', 'NOTE_G4', '-4', 'NOTE_C4', '-4', 'NOTE_DS4', '16', 'NOTE_F4', '16', 'NOTE_G4', '4', 'NOTE_C4', '4', 'NOTE_DS4', '16', 'NOTE_F4', '16', 'NOTE_D4', '-1', 'NOTE_F4', '-4', 'NOTE_AS3', '-4', 'NOTE_DS4', '16', 'NOTE_D4', '16', 'NOTE_F4', '4', 'NOTE_AS3', '-4', 'NOTE_DS4', '16', 'NOTE_D4', '16', 'NOTE_C4', '-1', 'NOTE_G4', '-4', 'NOTE_C4', '-4', 'NOTE_DS4', '16', 'NOTE_F4', '16', 'NOTE_G4', '4', 'NOTE_C4', '4', 'NOTE_DS4', '16', 'NOTE_F4', '16', 'NOTE_D4', '-2', 'NOTE_F4', '-4', 'NOTE_AS3', '-4', 'NOTE_D4', '-8', 'NOTE_DS4', '-8', 'NOTE_D4', '-8', 'NOTE_AS3', '-8', 'NOTE_C4', '-1', 'NOTE_C5', '-2', 'NOTE_AS4', '-2', 'NOTE_C4', '-2', 'NOTE_G4', '-2', 'NOTE_DS4', '-2', 'NOTE_DS4', '-4', 'NOTE_F4', '-4', 'NOTE_G4', '-1', 'NOTE_C5', '-2', 'NOTE_AS4', '-2', 'NOTE_C4', '-2', 'NOTE_G4', '-2', 'NOTE_DS4', '-2', 'NOTE_DS4', '-4', 'NOTE_D4', '-4', 'NOTE_C5', '8', 'NOTE_G4', '8', 'NOTE_GS4', '16', 'NOTE_AS4', '16', 'NOTE_C5', '8', 'NOTE_G4', '8', 'NOTE_GS4', '16', 'NOTE_AS4', '16', 'NOTE_C5', '8', 'NOTE_G4', '8', 'NOTE_GS4', '16', 'NOTE_AS4', '16', 'NOTE_C5', '8', 'NOTE_G4', '8', 'NOTE_GS4', '16', 'NOTE_AS4', '16', 'REST', '4', 'NOTE_GS5', '16', 'NOTE_AS5', '16', 'NOTE_C6', '8', 'NOTE_G5', '8', 'NOTE_GS5', '16', 'NOTE_AS5', '16', 'NOTE_C6', '8', 'NOTE_G5', '16', 'NOTE_GS5', '16', 'NOTE_AS5', '16', 'NOTE_C6', '8', 'NOTE_G5', '8', 'NOTE_GS5', '16', 'NOTE_AS5', '16']
// Greensleeves
// Score available at https://musescore.com/user/168402/scores/1396946
// notes = ['Greensleeves', 70, 'NOTE_G4', '8', 'NOTE_AS4', '4', 'NOTE_C5', '8', 'NOTE_D5', '-8', 'NOTE_DS5', '16', 'NOTE_D5', '8', 'NOTE_C5', '4', 'NOTE_A4', '8', 'NOTE_F4', '-8', 'NOTE_G4', '16', 'NOTE_A4', '8', 'NOTE_AS4', '4', 'NOTE_G4', '8', 'NOTE_G4', '-8', 'NOTE_FS4', '16', 'NOTE_G4', '8', 'NOTE_A4', '4', 'NOTE_FS4', '8', 'NOTE_D4', '4', 'NOTE_G4', '8', 'NOTE_AS4', '4', 'NOTE_C5', '8', 'NOTE_D5', '-8', 'NOTE_DS5', '16', 'NOTE_D5', '8', 'NOTE_C5', '4', 'NOTE_A4', '8', 'NOTE_F4', '-8', 'NOTE_G4', '16', 'NOTE_A4', '8', 'NOTE_AS4', '-8', 'NOTE_A4', '16', 'NOTE_G4', '8', 'NOTE_FS4', '-8', 'NOTE_E4', '16', 'NOTE_FS4', '8', 'NOTE_G4', '-2', 'NOTE_F5', '2', 'NOTE_E5', '16', 'NOTE_D5', '8', 'NOTE_C5', '4', 'NOTE_A4', '8', 'NOTE_F4', '-8', 'NOTE_G4', '16', 'NOTE_A4', '8', 'NOTE_AS4', '4', 'NOTE_G4', '8', 'NOTE_G4', '-8', 'NOTE_FS4', '16', 'NOTE_G4', '8', 'NOTE_A4', '4', 'NOTE_FS4', '8', 'NOTE_D4', '04', 'NOTE_F5', '2', 'NOTE_E5', '16', 'NOTE_D5', '8', 'NOTE_C5', '4', 'NOTE_A4', '8', 'NOTE_F4', '-8', 'NOTE_G4', '16', 'NOTE_A4', '8', 'NOTE_AS4', '-8', 'NOTE_A4', '16', 'NOTE_G4', '8', 'NOTE_FS4', '-8', 'NOTE_E4', '16', 'NOTE_FS4', '8', 'NOTE_G4', '-2', 'NOTE_G4', '8', 'NOTE_AS4', '4', 'NOTE_C5', '8', 'NOTE_D5', '-8', 'NOTE_DS5', '16', 'NOTE_D5', '8', 'NOTE_C5', '4', 'NOTE_A4', '8', 'NOTE_F4', '-8', 'NOTE_G4', '16', 'NOTE_A4', '8', 'NOTE_AS4', '4', 'NOTE_G4', '8', 'NOTE_G4', '-8', 'NOTE_FS4', '16', 'NOTE_G4', '8', 'NOTE_A4', '4', 'NOTE_FS4', '8', 'NOTE_D4', '4', 'NOTE_G4', '8', 'NOTE_AS4', '4', 'NOTE_C5', '8', 'NOTE_D5', '-8', 'NOTE_DS5', '16', 'NOTE_D5', '8', 'NOTE_C5', '4', 'NOTE_A4', '8', 'NOTE_F4', '-8', 'NOTE_G4', '16', 'NOTE_A4', '8', 'NOTE_AS4', '-8', 'NOTE_A4', '16', 'NOTE_G4', '8', 'NOTE_FS4', '-8', 'NOTE_E4', '16', 'NOTE_FS4', '8', 'NOTE_G4', '-2', 'NOTE_F5', '2', 'NOTE_E5', '16', 'NOTE_D5', '8', 'NOTE_C5', '4', 'NOTE_A4', '8', 'NOTE_F4', '-8', 'NOTE_G4', '16', 'NOTE_A4', '8', 'NOTE_AS4', '4', 'NOTE_G4', '8', 'NOTE_G4', '-8', 'NOTE_FS4', '16', 'NOTE_G4', '8', 'NOTE_A4', '4', 'NOTE_FS4', '8', 'NOTE_D4', '04', 'NOTE_F5', '2', 'NOTE_E5', '16', 'NOTE_D5', '8', 'NOTE_C5', '4', 'NOTE_A4', '8', 'NOTE_F4', '-8', 'NOTE_G4', '16', 'NOTE_A4', '8', 'NOTE_AS4', '-8', 'NOTE_A4', '16', 'NOTE_G4', '8', 'NOTE_FS4', '-8', 'NOTE_E4', '16', 'NOTE_FS4', '8', 'NOTE_G4', '-2']
// Green Hill Zone - Sonic the Hedgehog
// Score available at https://musescore.com/user/248346/scores/461661
// notes = ['Green Hill Zone - Sonic the Hedgehog', 140, 'REST', '2', 'NOTE_D5', '8', 'NOTE_B4', '4', 'NOTE_D5', '8', 'NOTE_CS5', '4', 'NOTE_D5', '8', 'NOTE_CS5', '4', 'NOTE_A4', '2', 'REST', '8', 'NOTE_A4', '8', 'NOTE_FS5', '8', 'NOTE_E5', '4', 'NOTE_D5', '8', 'NOTE_CS5', '4', 'NOTE_D5', '8', 'NOTE_CS5', '4', 'NOTE_A4', '2', 'REST', '4', 'NOTE_D5', '8', 'NOTE_B4', '4', 'NOTE_D5', '8', 'NOTE_CS5', '4', 'NOTE_D5', '8', 'NOTE_CS5', '4', 'NOTE_A4', '2', 'REST', '8', 'NOTE_B4', '8', 'NOTE_B4', '8', 'NOTE_G4', '4', 'NOTE_B4', '8', 'NOTE_A4', '4', 'NOTE_B4', '8', 'NOTE_A4', '4', 'NOTE_D4', '2', 'REST', '4', 'NOTE_D5', '8', 'NOTE_B4', '4', 'NOTE_D5', '8', 'NOTE_CS5', '4', 'NOTE_D5', '8', 'NOTE_CS5', '4', 'NOTE_A4', '2', 'REST', '8', 'NOTE_A4', '8', 'NOTE_FS5', '8', 'NOTE_E5', '4', 'NOTE_D5', '8', 'NOTE_CS5', '4', 'NOTE_D5', '8', 'NOTE_CS5', '4', 'NOTE_A4', '2', 'REST', '4', 'NOTE_D5', '8', 'NOTE_B4', '4', 'NOTE_D5', '8', 'NOTE_CS5', '4', 'NOTE_D5', '8', 'NOTE_CS5', '4', 'NOTE_A4', '2', 'REST', '8', 'NOTE_B4', '8', 'NOTE_B4', '8', 'NOTE_G4', '4', 'NOTE_B4', '8', 'NOTE_A4', '4', 'NOTE_B4', '8', 'NOTE_A4', '4', 'NOTE_D4', '8', 'NOTE_D4', '8', 'NOTE_FS4', '8', 'NOTE_E4', '-1', 'REST', '8', 'NOTE_D4', '8', 'NOTE_E4', '8', 'NOTE_FS4', '-1', 'REST', '8', 'NOTE_D4', '8', 'NOTE_D4', '8', 'NOTE_FS4', '8', 'NOTE_F4', '-1', 'REST', '8', 'NOTE_D4', '8', 'NOTE_F4', '8', 'NOTE_E4', '-1', 'REST', '2', 'NOTE_D5', '8', 'NOTE_B4', '4', 'NOTE_D5', '8', 'NOTE_CS5', '4', 'NOTE_D5', '8', 'NOTE_CS5', '4', 'NOTE_A4', '2', 'REST', '8', 'NOTE_A4', '8', 'NOTE_FS5', '8', 'NOTE_E5', '4', 'NOTE_D5', '8', 'NOTE_CS5', '4', 'NOTE_D5', '8', 'NOTE_CS5', '4', 'NOTE_A4', '2', 'REST', '4', 'NOTE_D5', '8', 'NOTE_B4', '4', 'NOTE_D5', '8', 'NOTE_CS5', '4', 'NOTE_D5', '8', 'NOTE_CS5', '4', 'NOTE_A4', '2', 'REST', '8', 'NOTE_B4', '8', 'NOTE_B4', '8', 'NOTE_G4', '4', 'NOTE_B4', '8', 'NOTE_A4', '4', 'NOTE_B4', '8', 'NOTE_A4', '4', 'NOTE_D4', '2', 'REST', '4', 'NOTE_D5', '8', 'NOTE_B4', '4', 'NOTE_D5', '8', 'NOTE_CS5', '4', 'NOTE_D5', '8', 'NOTE_CS5', '4', 'NOTE_A4', '2', 'REST', '8', 'NOTE_A4', '8', 'NOTE_FS5', '8', 'NOTE_E5', '4', 'NOTE_D5', '8', 'NOTE_CS5', '4', 'NOTE_D5', '8', 'NOTE_CS5', '4', 'NOTE_A4', '2', 'REST', '4', 'NOTE_D5', '8', 'NOTE_B4', '4', 'NOTE_D5', '8', 'NOTE_CS5', '4', 'NOTE_D5', '8', 'NOTE_CS5', '4', 'NOTE_A4', '2', 'REST', '8', 'NOTE_B4', '8', 'NOTE_B4', '8', 'NOTE_G4', '4', 'NOTE_B4', '8', 'NOTE_A4', '4', 'NOTE_B4', '8', 'NOTE_A4', '4', 'NOTE_D4', '8', 'NOTE_D4', '8', 'NOTE_FS4', '8', 'NOTE_E4', '-1', 'REST', '8', 'NOTE_D4', '8', 'NOTE_E4', '8', 'NOTE_FS4', '-1', 'REST', '8', 'NOTE_D4', '8', 'NOTE_D4', '8', 'NOTE_FS4', '8', 'NOTE_F4', '-1', 'REST', '8', 'NOTE_D4', '8', 'NOTE_F4', '8', 'NOTE_E4', '8', 'NOTE_E4', '-2', 'NOTE_A4', '8', 'NOTE_CS5', '8', 'NOTE_FS5', '8', 'NOTE_E5', '4', 'NOTE_D5', '8', 'NOTE_A5', '-4']
// The Legend of Zelda theme
// Based on the arrangement at https://www.flutetunes.com/tunes.php?id=169
// notes = ['The Legend of Zelda theme', 88, 'NOTE_AS4', '-2', 'NOTE_F4', '8', 'NOTE_F4', '8', 'NOTE_AS4', '8', 'NOTE_GS4', '16', 'NOTE_FS4', '16', 'NOTE_GS4', '-2', 'NOTE_AS4', '-2', 'NOTE_FS4', '8', 'NOTE_FS4', '8', 'NOTE_AS4', '8', 'NOTE_A4', '16', 'NOTE_G4', '16', 'NOTE_A4', '-2', 'REST', '1', 'NOTE_AS4', '4', 'NOTE_F4', '-4', 'NOTE_AS4', '8', 'NOTE_AS4', '16', 'NOTE_C5', '16', 'NOTE_D5', '16', 'NOTE_DS5', '16', 'NOTE_F5', '2', 'NOTE_F5', '8', 'NOTE_F5', '8', 'NOTE_F5', '8', 'NOTE_FS5', '16', 'NOTE_GS5', '16', 'NOTE_AS5', '-2', 'NOTE_AS5', '8', 'NOTE_AS5', '8', 'NOTE_GS5', '8', 'NOTE_FS5', '16', 'NOTE_GS5', '-8', 'NOTE_FS5', '16', 'NOTE_F5', '2', 'NOTE_F5', '4', 'NOTE_DS5', '-8', 'NOTE_F5', '16', 'NOTE_FS5', '2', 'NOTE_F5', '8', 'NOTE_DS5', '8', 'NOTE_CS5', '-8', 'NOTE_DS5', '16', 'NOTE_F5', '2', 'NOTE_DS5', '8', 'NOTE_CS5', '8', 'NOTE_C5', '-8', 'NOTE_D5', '16', 'NOTE_E5', '2', 'NOTE_G5', '8', 'NOTE_F5', '16', 'NOTE_F4', '16', 'NOTE_F4', '16', 'NOTE_F4', '16', 'NOTE_F4', '16', 'NOTE_F4', '16', 'NOTE_F4', '16', 'NOTE_F4', '16', 'NOTE_F4', '8', 'NOTE_F4', '16', 'NOTE_F4', '8', 'NOTE_AS4', '4', 'NOTE_F4', '-4', 'NOTE_AS4', '8', 'NOTE_AS4', '16', 'NOTE_C5', '16', 'NOTE_D5', '16', 'NOTE_DS5', '16', 'NOTE_F5', '2', 'NOTE_F5', '8', 'NOTE_F5', '8', 'NOTE_F5', '8', 'NOTE_FS5', '16', 'NOTE_GS5', '16', 'NOTE_AS5', '-2', 'NOTE_CS6', '4', 'NOTE_C6', '4', 'NOTE_A5', '2', 'NOTE_F5', '4', 'NOTE_FS5', '-2', 'NOTE_AS5', '4', 'NOTE_A5', '4', 'NOTE_F5', '2', 'NOTE_F5', '4', 'NOTE_FS5', '-2', 'NOTE_AS5', '4', 'NOTE_A5', '4', 'NOTE_F5', '2', 'NOTE_D5', '4', 'NOTE_DS5', '-2', 'NOTE_FS5', '4', 'NOTE_F5', '4', 'NOTE_CS5', '2', 'NOTE_AS4', '4', 'NOTE_C5', '-8', 'NOTE_D5', '16', 'NOTE_E5', '2', 'NOTE_G5', '8', 'NOTE_F5', '16', 'NOTE_F4', '16', 'NOTE_F4', '16', 'NOTE_F4', '16', 'NOTE_F4', '16', 'NOTE_F4', '16', 'NOTE_F4', '16', 'NOTE_F4', '16', 'NOTE_F4', '8', 'NOTE_F4', '16', 'NOTE_F4', '8']
// Baby Elephant Walk
// Score available at https://musescore.com/user/7965776/scores/1862611
// notes = ['Baby Elephant Walk', 132, 'NOTE_C4', '-8', 'NOTE_E4', '16', 'NOTE_G4', '8', 'NOTE_C5', '8', 'NOTE_E5', '8', 'NOTE_D5', '8', 'NOTE_C5', '8', 'NOTE_A4', '8', 'NOTE_FS4', '8', 'NOTE_G4', '8', 'REST', '4', 'REST', '2', 'NOTE_C4', '-8', 'NOTE_E4', '16', 'NOTE_G4', '8', 'NOTE_C5', '8', 'NOTE_E5', '8', 'NOTE_D5', '8', 'NOTE_C5', '8', 'NOTE_A4', '8', 'NOTE_G4', '-2', 'NOTE_A4', '8', 'NOTE_DS4', '1', 'NOTE_A4', '8', 'NOTE_E4', '8', 'NOTE_C4', '8', 'REST', '4', 'REST', '2', 'NOTE_C4', '-8', 'NOTE_E4', '16', 'NOTE_G4', '8', 'NOTE_C5', '8', 'NOTE_E5', '8', 'NOTE_D5', '8', 'NOTE_C5', '8', 'NOTE_A4', '8', 'NOTE_FS4', '8', 'NOTE_G4', '8', 'REST', '4', 'REST', '4', 'REST', '8', 'NOTE_G4', '8', 'NOTE_D5', '4', 'NOTE_D5', '4', 'NOTE_B4', '8', 'NOTE_G4', '8', 'REST', '8', 'NOTE_G4', '8', 'NOTE_C5', '4', 'NOTE_C5', '4', 'NOTE_AS4', '16', 'NOTE_C5', '16', 'NOTE_AS4', '16', 'NOTE_G4', '16', 'NOTE_F4', '8', 'NOTE_DS4', '8', 'NOTE_FS4', '4', 'NOTE_FS4', '4', 'NOTE_F4', '16', 'NOTE_G4', '16', 'NOTE_F4', '16', 'NOTE_DS4', '16', 'NOTE_C4', '8', 'NOTE_G4', '8', 'NOTE_AS4', '8', 'NOTE_C5', '8', 'REST', '4', 'REST', '2']
// Bloody Tears (Castlevania II)
// https://musescore.com/user/263171/scores/883296
// notes = ['Bloody Tears (Castlevania II)', 144, 'REST', '4', 'NOTE_G5', '4', 'NOTE_A5', '4', 'NOTE_AS5', '4', 'NOTE_A5', '4', 'NOTE_F5', '4', 'NOTE_A5', '4', 'NOTE_G5', '4', 'REST', '4', 'NOTE_G5', '4', 'NOTE_A5', '4', 'NOTE_AS5', '4', 'NOTE_C6', '4', 'NOTE_AS5', '4', 'NOTE_A5', '4', 'NOTE_G5', '4', 'REST', '4', 'NOTE_G5', '4', 'NOTE_A5', '4', 'NOTE_AS5', '4', 'NOTE_A5', '4', 'NOTE_F5', '4', 'NOTE_A5', '4', 'NOTE_G5', '4', 'NOTE_D6', '4', 'REST', '8', 'NOTE_C6', '8', 'REST', '4', 'NOTE_AS5', '4', 'NOTE_A5', '4', 'NOTE_AS5', '8', 'NOTE_C6', '8', 'NOTE_F6', '8', 'REST', '8', 'REST', '4', 'NOTE_G5', '16', 'NOTE_D5', '16', 'NOTE_D6', '16', 'NOTE_D5', '16', 'NOTE_C6', '16', 'NOTE_D5', '16', 'NOTE_AS5', '16', 'NOTE_D5', '16', 'NOTE_A5', '16', 'NOTE_D5', '16', 'NOTE_AS5', '16', 'NOTE_D5', '16', 'NOTE_A5', '16', 'NOTE_D5', '16', 'NOTE_G5', '16', 'NOTE_D5', '16', 'NOTE_A5', '16', 'NOTE_D5', '16', 'NOTE_AS5', '16', 'NOTE_D5', '16', 'NOTE_C6', '16', 'NOTE_D5', '16', 'NOTE_AS5', '16', 'NOTE_D5', '16', 'NOTE_A5', '16', 'NOTE_D5', '16', 'NOTE_F5', '16', 'NOTE_D5', '16', 'NOTE_A5', '16', 'NOTE_D5', '16', 'NOTE_G5', '16', 'NOTE_D5', '16', 'NOTE_G5', '16', 'NOTE_D5', '16', 'NOTE_D6', '16', 'NOTE_D5', '16', 'NOTE_C6', '16', 'NOTE_D5', '16', 'NOTE_AS5', '16', 'NOTE_D5', '16', 'NOTE_A5', '16', 'NOTE_D5', '16', 'NOTE_AS5', '16', 'NOTE_D5', '16', 'NOTE_A5', '16', 'NOTE_D5', '16', 'NOTE_AS5', '16', 'NOTE_D5', '16', 'NOTE_A5', '16', 'NOTE_D5', '16', 'NOTE_AS5', '16', 'NOTE_D5', '16', 'NOTE_C6', '1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
', 'NOTE_AS4', '4', 'NOTE_A4', '8', 'NOTE_G4', '16', 'NOTE_C4', '8', 'NOTE_C4', '16', 'NOTE_G4', '16', 'NOTE_G4', '8', 'NOTE_G4', '16', 'NOTE_F4', '8', 'NOTE_E4', '8', 'NOTE_D4', '8', 'NOTE_C4', '-2', 'NOTE_C4', '16', 'NOTE_C4', '8', 'NOTE_C4', '16', 'NOTE_E4', '16', 'NOTE_E4', '8', 'NOTE_E4', '16', 'NOTE_F4', '16', 'NOTE_F4', '8', 'NOTE_F4', '16', 'NOTE_FS4', '16', 'NOTE_FS4', '8', 'NOTE_FS4', '16', 'NOTE_G4', '8', 'REST', '8', 'NOTE_AS4', '8', 'NOTE_C5', '1']
// Vampire Killer (Castlevania)
// Score available at https://musescore.com/user/28972071/scores/5425616
// notes = ['Vampire Killer (Castlevania)', 130, 'NOTE_E5', '16', 'NOTE_E5', '8', 'NOTE_D5', '16', 'REST', '16', 'NOTE_CS5', '-4', 'NOTE_E4', '8', 'NOTE_FS4', '16', 'NOTE_G4', '16', 'NOTE_A4', '16', 'NOTE_B4', '-8', 'NOTE_E4', '-8', 'NOTE_B4', '8', 'NOTE_A4', '16', 'NOTE_D5', '-4', 'NOTE_E5', '16', 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
// Never Gonna Give You Up - Rick Astley
// Score available at https://musescore.com/chlorondria_5/never-gonna-give-you-up_alto-sax
// notes = ['Never Gonna Give You Up - Rick Astley', 114, 'NOTE_D5', '-4', 'NOTE_E5', '-4', 'NOTE_A4', '4', 'NOTE_E5', '-4', 'NOTE_FS5', '-4', 'NOTE_A5', '16', 'NOTE_G5', '16', 'NOTE_FS5', '8', 'NOTE_D5', '-4', 'NOTE_E5', '-4', 'NOTE_A4', '2', 'NOTE_A4', '16', 'NOTE_A4', '16', 'NOTE_B4', '16', 'NOTE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
// Prince Igor - Polovtsian Dances, Borodin
// notes = ['Prince Igor - Polovtsian Dances, Borodin', 110, 'NOTE_G4', '4', 'NOTE_G4', '4', 'NOTE_D5', '-2', 'NOTE_C5', '8', 'NOTE_D5', '8', 'NOTE_AS4', '4', 'NOTE_A4', '8', 'NOTE_G4', '8', 'NOTE_A4', '8', 'NOTE_AS4', '8', 'NOTE_C5', '1', 'NOTE_D5', '4', 'NOTE_A4', '4', 'NOTE_G4', '8', 'NOTE_F4', '8', 'NOTE_D4', '4', 'NOTE_D4', '4', 'NOTE_G4', '-2', 'NOTE_A4', '4', 'NOTE_G4', '4', 'NOTE_F4', '8', 'NOTE_E4', '8', 'NOTE_F4', '4', 'NOTE_E4', '4', 'NOTE_D4', '1', 'NOTE_E4', '4', 'NOTE_F4', '4', 'NOTE_A4', '4', 'NOTE_G4', '4', 'NOTE_G4', '4', 'NOTE_AS4', '-2', 'NOTE_C5', '4', 'NOTE_AS4', '4', 'NOTE_A4', '8', 'NOTE_G4', '8', 'NOTE_A4', '4', 'NOTE_AS4', '4', 'NOTE_C5', '-2', 'NOTE_CS5', '4', 'NOTE_C5', '4', 'NOTE_A4', '4', 'NOTE_CS5', '4', 'NOTE_CS4', '4', 'NOTE_F5', '-2', 'NOTE_G5', '4', 'NOTE_F5', '4', 'NOTE_DS4', '8', 'NOTE_CS4', '8', 'NOTE_F5', '2', 'NOTE_C5', '-2', 'NOTE_AS4', '4', 'NOTE_C5', '4', 'NOTE_AS4', '8', 'NOTE_A4', '8', 'NOTE_G4', '4', 'NOTE_G4', '4', 'NOTE_AS4', '1', 'NOTE_C5', '4', 'NOTE_AS4', '4', 'NOTE_A4', '8', 'NOTE_G4', '8', 'NOTE_F4', '4', 'NOTE_G4', '4', 'NOTE_A4', '1', 'NOTE_AS4', '4', 'NOTE_A4', '4', 'NOTE_F4', '4', 'NOTE_G4', '4', 'NOTE_G4', '4', 'NOTE_D5', '-2', 'NOTE_C5', '4', 'NOTE_AS4', '4', 'NOTE_A4', '8', 'NOTE_G4', '8', 'NOTE_A4', '-1', 'NOTE_A4', '-1', 'REST', '2', 'NOTE_G4', '4', 'NOTE_G4', '4', 'NOTE_D5', '-2', 'NOTE_C5', '8', 'NOTE_D5', '8', 'NOTE_AS4', '4', 'NOTE_A4', '8', 'NOTE_G4', '8', 'NOTE_A4', '8', 'NOTE_AS4', '8', 'NOTE_C5', '1', 'NOTE_C5', '8', 'NOTE_D5', '8', 'NOTE_C5', '4', 'NOTE_AS4', '8', 'NOTE_A4', '8', 'NOTE_D4', '4', 'NOTE_D4', '4', 'NOTE_G4', '-2', 'NOTE_G4', '8', 'NOTE_A4', '8', 'NOTE_G4', '4', 'NOTE_F4', '8', 'NOTE_E4', '8', 'NOTE_F4', '8', 'NOTE_E4', '8', 'NOTE_D4', '-2', 'REST', '4', 'NOTE_C5', '8', 'NOTE_D5', '8', 'NOTE_C5', '4', 'NOTE_AS4', '8', 'NOTE_A4', '8', 'NOTE_G4', '4', 'NOTE_G4', '4', 'NOTE_B4', '-2', 'NOTE_C5', '4', 'NOTE_AS4', '4', 'NOTE_A4', '8', 'NOTE_G4', '8', 'NOTE_A4', '4', 'NOTE_G4', '4', 'NOTE_F4', '-1', 'REST', '4', 'NOTE_G4', '4', 'NOTE_G4', '4', 'NOTE_D5', '-2', 'NOTE_C5', '8', 'NOTE_D5', '8', 'NOTE_AS4', '4', 'NOTE_A4', '8', 'NOTE_G4', '8', 'NOTE_A4', '4', 'NOTE_G4', '4', 'NOTE_F4', '-2', 'NOTE_A4', '4', 'NOTE_G4', '4', 'NOTE_F4', '-2', 'NOTE_A4', '4', 'NOTE_G4', '4', 'NOTE_F4', '-1']
// Zelda's Lullaby (The Legend of Zelda, Ocarina of Time)
// Score available at https://musescore.com/user/12754451/scores/2762776
// notes = ['Zelda\'s Lullaby - The Legend of Zelda, Ocarina of Time', 108, 'NOTE_E4', '2', 'NOTE_G4', '4', 'NOTE_D4', '2', 'NOTE_C4', '8', 'NOTE_D4', '8', 'NOTE_E4', '2', 'NOTE_G4', '4', 'NOTE_D4', '-2', 'NOTE_E4', '2', 'NOTE_G4', '4', 'NOTE_D5', '2', 'NOTE_C5', '4', 'NOTE_G4', '2', 'NOTE_F4', '8', 'NOTE_E4', '8', 'NOTE_D4', '-2', 'NOTE_E4', '2', 'NOTE_G4', '4', 'NOTE_D4', '2', 'NOTE_C4', '8', 'NOTE_D4', '8', 'NOTE_E4', '2', 'NOTE_G4', '4', 'NOTE_D4', '-2', 'NOTE_E4', '2', 'NOTE_G4', '4', 'NOTE_D5', '2', 'NOTE_C5', '4', 'NOTE_G4', '2', 'NOTE_F4', '8', 'NOTE_E4', '8', 'NOTE_F4', '8', 'NOTE_E4', '8', 'NOTE_C4', '2', 'NOTE_F4', '2', 'NOTE_E4', '8', 'NOTE_D4', '8', 'NOTE_E4', '8', 'NOTE_D4', '8', 'NOTE_A3', '2', 'NOTE_G4', '2', 'NOTE_F4', '8', 'NOTE_E4', '8', 'NOTE_F4', '8', 'NOTE_E4', '8', 'NOTE_C4', '4', 'NOTE_F4', '4', 'NOTE_C5', '-2']
// Super Mario Bros theme, by Koji Kondo
// Score available at https://musescore.com/user/2123/scores/2145
// notes = ['Super Mario Bros theme, by Koji Kondo', 200, 'NOTE_E5', '8', 'NOTE_E5', '8', 'REST', '8', 'NOTE_E5', '8', 'REST', '8', 'NOTE_C5', '8', 'NOTE_E5', '8', 'NOTE_G5', '4', 'REST', '4', 'NOTE_G4', '8', 'REST', '4', 'NOTE_C5', '-4', 'NOTE_G4', '8', 'REST', '4', 'NOTE_E4', '-4', 'NOTE_A4', '4',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
// Asa branca - Luiz Gonzaga
// Score available at https://musescore.com/user/190926/scores/181370
// notes = ['Asa branca - Luiz Gonzaga', 120, 'NOTE_G4', '8', 'NOTE_A4', '8', 'NOTE_B4', '4', 'NOTE_D5', '4', 'NOTE_D5', '4', 'NOTE_B4', '4', 'NOTE_C5', '4', 'NOTE_C5', '2', 'NOTE_G4', '8', 'NOTE_A4', '8', 'NOTE_B4', '4', 'NOTE_D5', '4', 'NOTE_D5', '4', 'NOTE_C5', '4', 'NOTE_B4', '2', 'REST', '8', 'NOTE_G4', '8', 'NOTE_G4', '8', 'NOTE_A4', '8', 'NOTE_B4', '4', 'NOTE_D5', '4', 'REST', '8', 'NOTE_D5', '8', 'NOTE_C5', '8', 'NOTE_B4', '8', 'NOTE_G4', '4', 'NOTE_C5', '4', 'REST', '8', 'NOTE_C5', '8', 'NOTE_B4', '8', 'NOTE_A4', '8', 'NOTE_A4', '4', 'NOTE_B4', '4', 'REST', '8', 'NOTE_B4', '8', 'NOTE_A4', '8', 'NOTE_G4', '8', 'NOTE_G4', '2', 'REST', '8', 'NOTE_G4', '8', 'NOTE_G4', '8', 'NOTE_A4', '8', 'NOTE_B4', '4', 'NOTE_D5', '4', 'REST', '8', 'NOTE_D5', '8', 'NOTE_C5', '8', 'NOTE_B4', '8', 'NOTE_G4', '4', 'NOTE_C5', '4', 'REST', '8', 'NOTE_C5', '8', 'NOTE_B4', '8', 'NOTE_A4', '8', 'NOTE_A4', '4', 'NOTE_B4', '4', 'REST', '8', 'NOTE_B4', '8', 'NOTE_A4', '8', 'NOTE_G4', '8', 'NOTE_G4', '4', 'NOTE_F5', '8', 'NOTE_D5', '8', 'NOTE_E5', '8', 'NOTE_C5', '8', 'NOTE_D5', '8', 'NOTE_B4', '8', 'NOTE_C5', '8', 'NOTE_A4', '8', 'NOTE_B4', '8', 'NOTE_G4', '8', 'NOTE_A4', '8', 'NOTE_G4', '8', 'NOTE_E4', '8', 'NOTE_G4', '8', 'NOTE_G4', '4', 'NOTE_F5', '8', 'NOTE_D5', '8', 'NOTE_E5', '8', 'NOTE_C5', '8', 'NOTE_D5', '8', 'NOTE_B4', '8', 'NOTE_C5', '8', 'NOTE_A4', '8', 'NOTE_B4', '8', 'NOTE_G4', '8', 'NOTE_A4', '8', 'NOTE_G4', '8', 'NOTE_E4', '8', 'NOTE_G4', '8', 'NOTE_G4', '-2', 'REST', '4']
// The Godfather theme
// Score available at https://musescore.com/user/35463/scores/55160
// notes = ['The Godfather theme', 80, 'REST', '4', 'REST', '8', 'REST', '8', 'REST', '8', 'NOTE_E4', '8', 'NOTE_A4', '8', 'NOTE_C5', '8', 'NOTE_B4', '8', 'NOTE_A4', '8', 'NOTE_C5', '8', 'NOTE_A4', '8', 'NOTE_B4', '8', 'NOTE_A4', '8', 'NOTE_F4', '8', 'NOTE_G4', '8', 'NOTE_E4', '2', 'NOTE_E4', '8', 'NOTE_A4', '8', 'NOTE_C5', '8', 'NOTE_B4', '8', 'NOTE_A4', '8', 'NOTE_C5', '8', 'NOTE_A4', '8', 'NOTE_C5', '8', 'NOTE_A4', '8', 'NOTE_E4', '8', 'NOTE_DS4', '8', 'NOTE_D4', '2', 'NOTE_D4', '8', 'NOTE_F4', '8', 'NOTE_GS4', '8', 'NOTE_B4', '2', 'NOTE_D4', '8', 'NOTE_F4', '8', 'NOTE_GS4', '8', 'NOTE_A4', '2', 'NOTE_C4', '8', 'NOTE_C4', '8', 'NOTE_G4', '8', 'NOTE_F4', '8', 'NOTE_E4', '8', 'NOTE_G4', '8', 'NOTE_F4', '8', 'NOTE_F4', '8', 'NOTE_E4', '8', 'NOTE_E4', '8', 'NOTE_GS4', '8', 'NOTE_A4', '2', 'REST', '8', 'NOTE_A4', '8', 'NOTE_A4', '8', 'NOTE_GS4', '8', 'NOTE_G4', '2', 'NOTE_B4', '8', 'NOTE_A4', '8', 'NOTE_F4', '8', 'NOTE_E4', '2', 'NOTE_E4', '8', 'NOTE_G4', '8', 'NOTE_E4', '8', 'NOTE_D4', '2', 'NOTE_D4', '8', 'NOTE_D4', '8', 'NOTE_F4', '8', 'NOTE_DS4', '8', 'NOTE_E4', '2', 'REST', '8', 'NOTE_E4', '8', 'NOTE_A4', '8', 'NOTE_C5', '8', 'NOTE_B4', '8', 'NOTE_A4', '8', 'NOTE_C5', '8', 'NOTE_A4', '8', 'NOTE_B4', '8', 'NOTE_A4', '8', 'NOTE_F4', '8', 'NOTE_G4', '8', 'NOTE_E4', '2', 'NOTE_E4', '8', 'NOTE_A4', '8', 'NOTE_C5', '8', 'NOTE_B4', '8', 'NOTE_A4', '8', 'NOTE_C5', '8', 'NOTE_A4', '8', 'NOTE_C5', '8', 'NOTE_A4', '8', 'NOTE_E4', '8', 'NOTE_DS4', '8', 'NOTE_D4', '2', 'NOTE_D4', '8', 'NOTE_F4', '8', 'NOTE_GS4', '8', 'NOTE_B4', '2', 'NOTE_D4', '8', 'NOTE_F4', '8', 'NOTE_GS4', '8', 'NOTE_A4', '2', 'NOTE_C4', '8', 'NOTE_C4', '8', 'NOTE_G4', '8', 'NOTE_F4', '8', 'NOTE_E4', '8', 'NOTE_G4', '8', 'NOTE_F4', '8', 'NOTE_F4', '8', 'NOTE_E4', '8', 'NOTE_E4', '8', 'NOTE_GS4', '8', 'NOTE_A4', '2', 'REST', '8', 'NOTE_A4', '8', 'NOTE_A4', '8', 'NOTE_GS4', '8', 'NOTE_G4', '2', 'NOTE_B4', '8', 'NOTE_A4', '8', 'NOTE_F4', '8', 'NOTE_E4', '2', 'NOTE_E4', '8', 'NOTE_G4', '8', 'NOTE_E4', '8', 'NOTE_D4', '2', 'NOTE_D4', '8', 'NOTE_D4', '8', 'NOTE_F4', '8', 'NOTE_DS4', '8', 'NOTE_E4', '2']
// Professor Layton's theme (Professor Layton and the Courious village)
// available at https://musescore.com/user/311366/scores/373161
// notes = ['Professor Layton\'s theme', 140, 'NOTE_D5', '1', 'NOTE_DS5', '1', 'NOTE_F5', '1', 'REST', '4', 'NOTE_F5', '-4', 'NOTE_DS5', '8', 'NOTE_D5', '8', 'NOTE_F5', '1', 'NOTE_AS4', '8', 'NOTE_G4', '-2', 'NOTE_F4', '1', 'NOTE_F4', '1', 'REST', '4', 'REST', '8', 'NOTE_F4', '8', 'NOTE_G4', '8', 'N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
