locked/picoclock/fw/src/system/filesystem.h

#ifndef FILESYSTEM_H
#define FILESYSTEM_H

#include <stdbool.h>
#include "system.h"

bool filesystem_read_config_file();
bool filesystem_fw_file_exists();
bool filesystem_read_fw_file(ota_segment_consumer_t process_ota_segment);
void filesystem_mount();
uint32_t filesystem_get_capacity();

bool filesystem_write_file(char *file_name);
void filesystem_write_bytes(char *buffer, uint16_t buffer_length);
void filesystem_close();
void filesystem_unmount();

#endif // FILESYSTEM_H
