locked/picoclock/fw/src/system/ui_task.h

#ifndef UI_TASK_H
#define UI_TASK_H

#include <stdint.h>

void init_ui();
void screen_shutdown();
void ui_refresh_screen(bool message_clear, time_struct dt);
void ui_btn_long_click(int btn, time_struct dt);
void ui_btn_click(int btn, time_struct dt);
void screen_anim();

#endif // UI_TASK_H
